Kononenko-K/Allwinner_H616_Devboard/pics/1.jpg

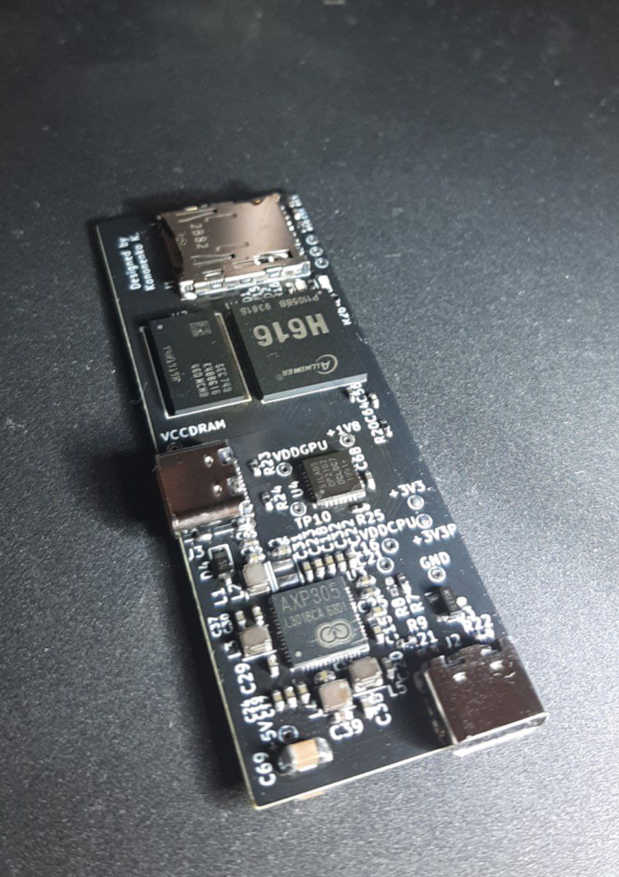
pics/1.jpg
